sophienyaa/Honda-Motorcycle-Dash/src/utils.h

float calcValueDivide256(int val);
float calcValueMinus40(int val);
float calcValueDivide10(int val);
float calcValueDivide10(int val);
float calcValueDivide16(int val);
uint8_t calcChecksum(const uint8_t* data, uint8_t len);
float calcKPHtoMPH(int val);
